CrazyRobMiles/RaspberryPi-DialTelephone/helpers/OutGPIO.js

const onoff = require('onoff'); //include onoff to interact with the GPIO

class OutGPIO {
    constructor(GPIONumber) {
        this.GPIONumber = GPIONumber;
    }

    init() {
//        console.log(`Initialising output GPIO ${this.GPIONumber}`);
        if(onoff.Gpio.accessible){
            this.gpio = new onoff.Gpio(this.GPIONumber, 'out'); 
        }
    }

    on(){
        if(onoff.Gpio.accessible){
            this.gpio.writeSync(1);
        }
    }

    pulse(){
        this.on();
        setTimeout(()=>{this.off();}, 1000);
    }

    off(){
        if(onoff.Gpio.accessible){
            this.gpio.writeSync(0);
        }
    }
}

module.exports = OutGPIO ;
